VorosEgyes/BirdNest/include/temperature.h

#pragma once

#include <stdint.h>

// ============================================================
// temperature.h
// DS18B20 temperature sensor over OneWire bus (TEMP_PIN).
// ============================================================

// Initialise the sensor. Call from setup().
void tempInit();

// Read temperature in Celsius.
// Returns -127.0 if the sensor is not reachable.
float tempRead();

// Diagnostics – available after tempInit().
uint8_t tempGetSensorCount();
bool    tempIsParasitePower();
